Antannah/signalrpi/doc/ebyte-07-m1101-sma_side-to-hole.jpg

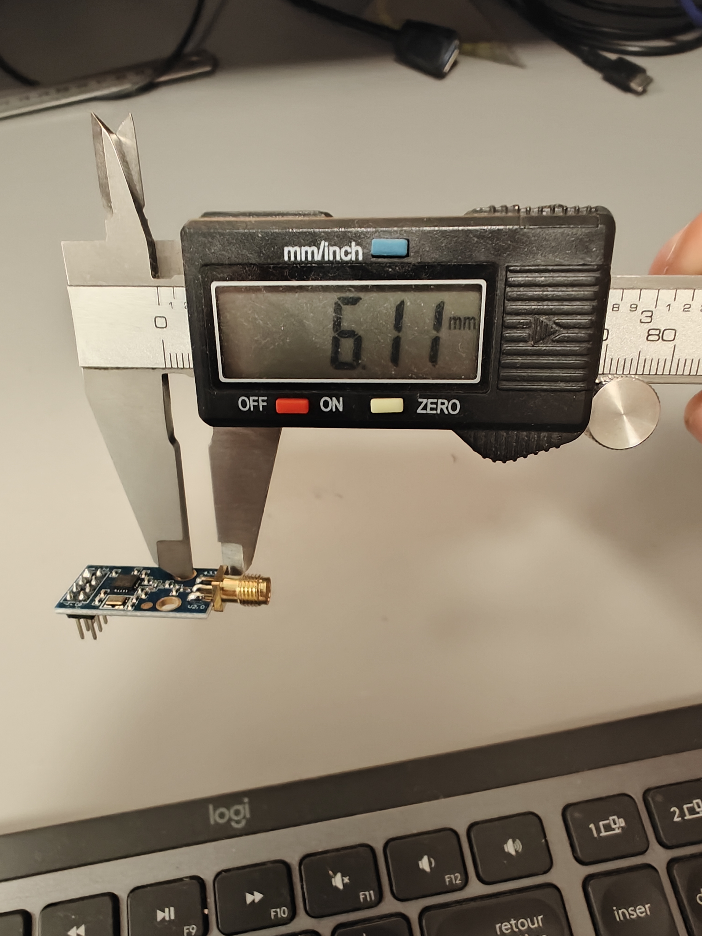
doc/ebyte-07-m1101-sma_side-to-hole.jpg
