Antannah/signalrpi/doc/image_2022-05-15_19-34-45.png

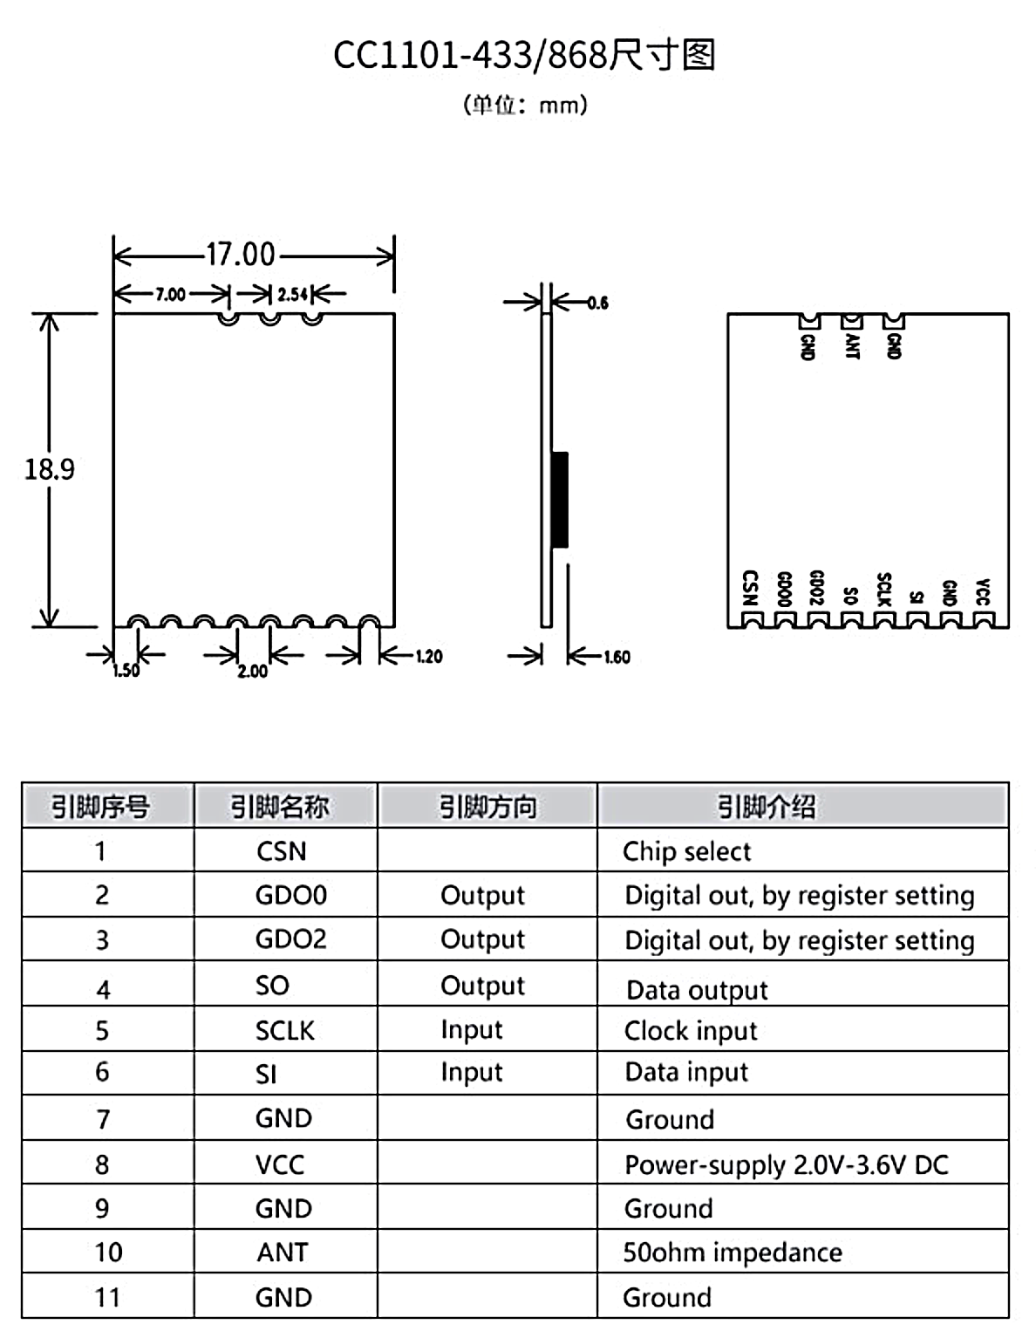
doc/image_2022-05-15_19-34-45.png
